MagnusThome/RejsaCAN-ESP32/Code Examples/RejsaCAN v3.x - ESP32-S3 - read rpm over BLE/Arduino IDE settings for ESP32-S3-WROOM-1-N16R8.png

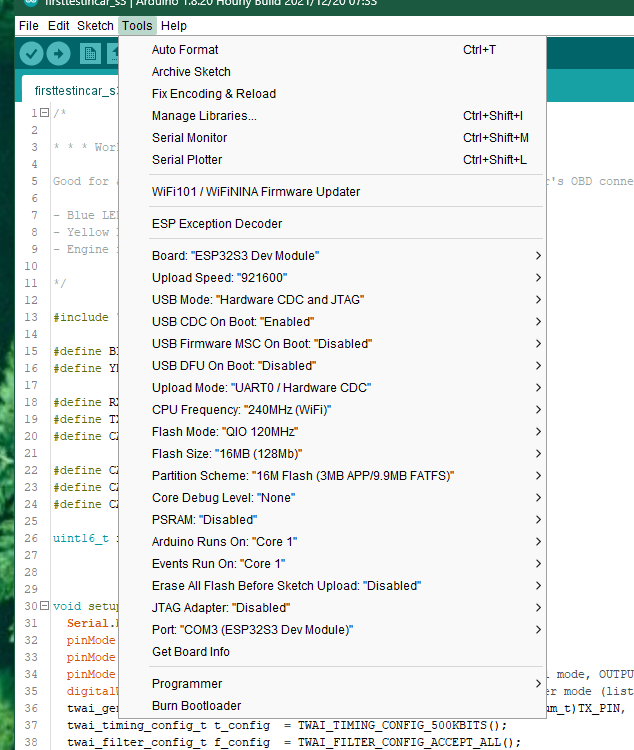
Code Examples/RejsaCAN v3.x - ESP32-S3 - read rpm over BLE/Arduino IDE settings for ESP32-S3-WROOM-1-N16R8.png
