MagnusThome/RejsaCAN-ESP32/Schematics/Schematic_RejsaCAN v2.1.png

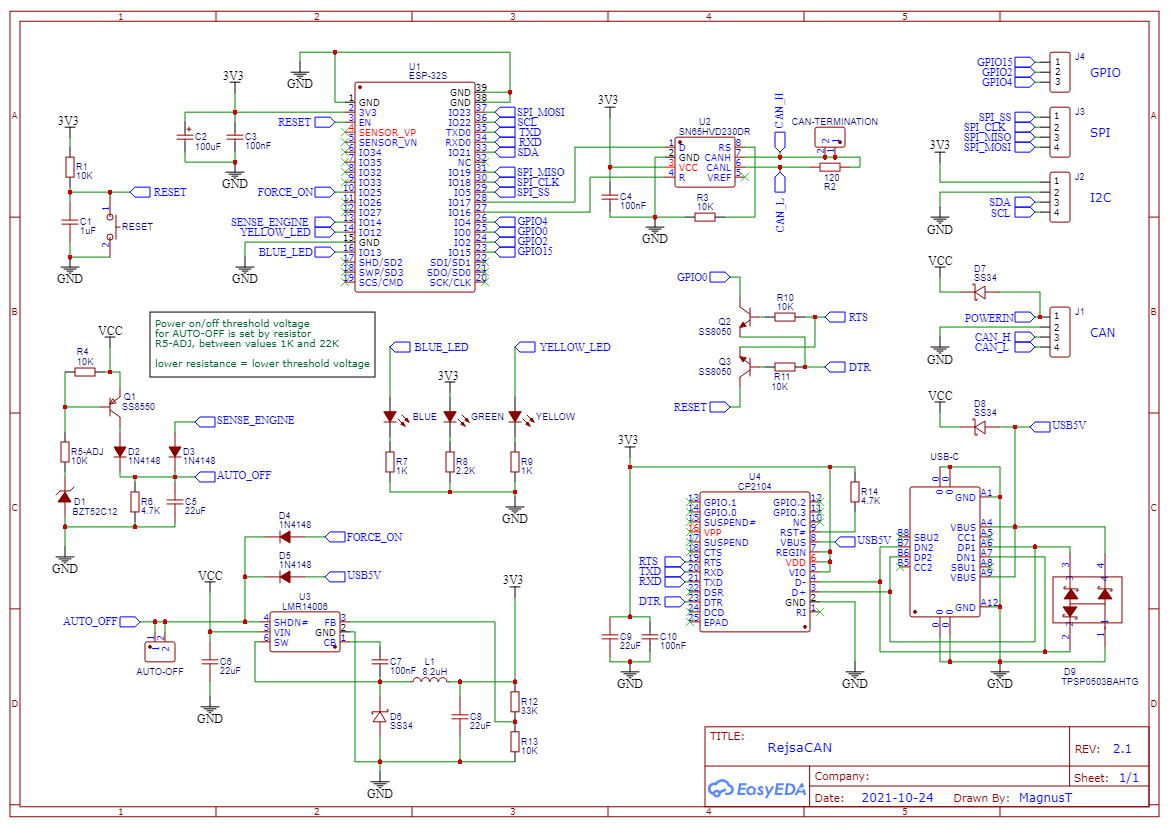
Schematics/Schematic_RejsaCAN v2.1.png
