MagnusThome/RejsaCAN-ESP32/Schematics/Schematic_RejsaCAN v2.2b.png

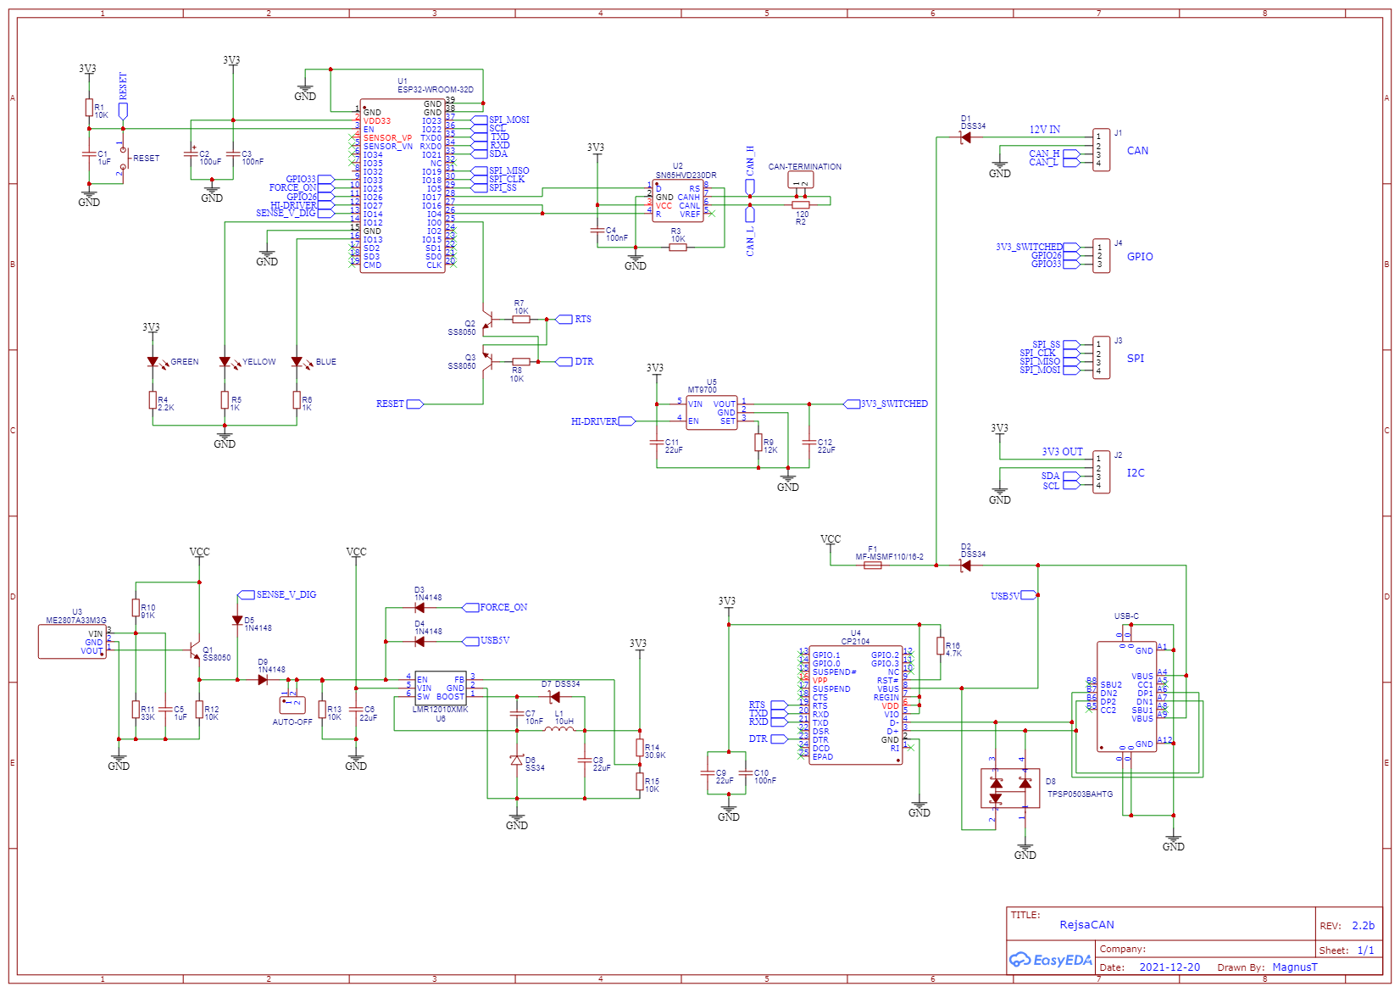
Schematics/Schematic_RejsaCAN v2.2b.png
