MagnusThome/RejsaCAN-ESP32/Schematics/Schematic_RejsaCAN v2.3.png

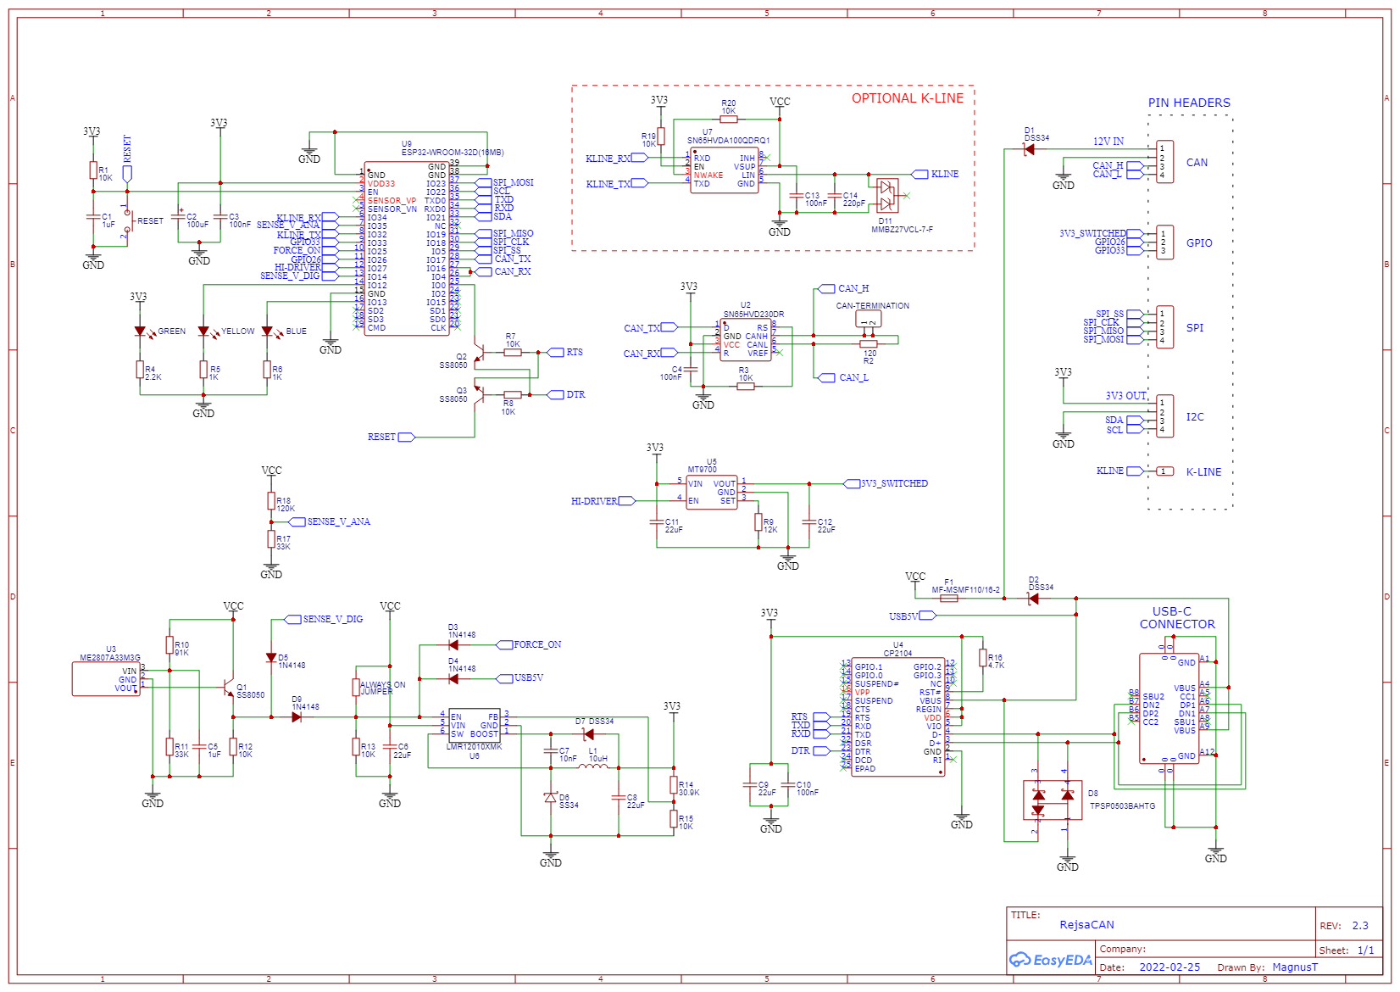
Schematics/Schematic_RejsaCAN v2.3.png
