MagnusThome/RejsaCAN-ESP32/Schematics/Schematic_RejsaCAN v3.0.png

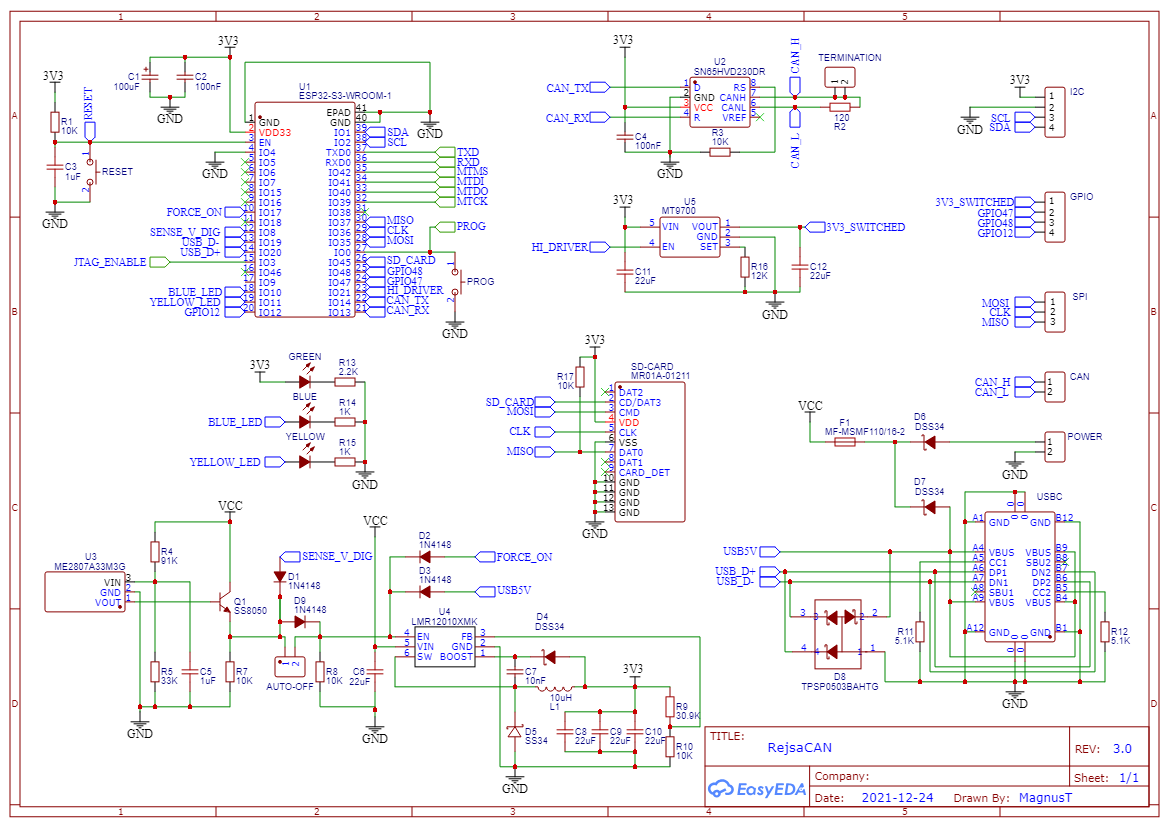
Schematics/Schematic_RejsaCAN v3.0.png
