MagnusThome/RejsaCAN-ESP32/3dprint/Small-flat-housing-LID.stl

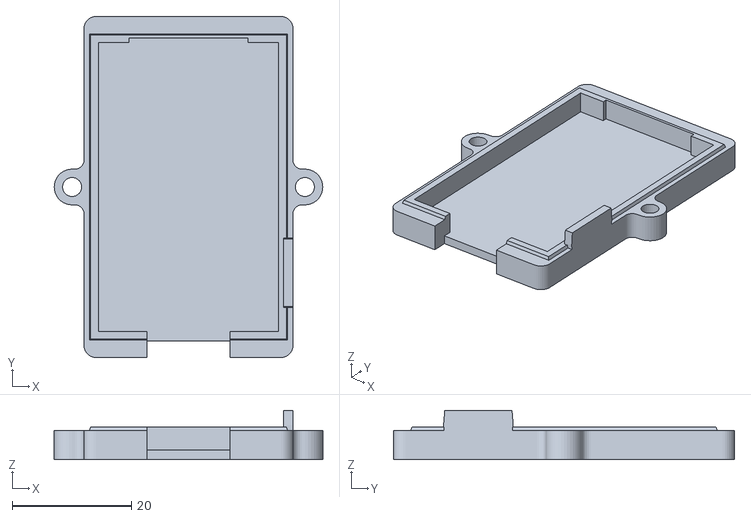
[picture p26: CAD file, 2021-10-26, last stored version]
3dprint/Small-flat-housing-LID.stl
45.1 x 57.2 x 8.30
