MagnusThome/RejsaCAN-ESP32/Code Examples/RejsaCAN v3.x - ESP32-S3 - read rpm over BLE/ble_uart.h

#include <BLEDevice.h>
#include <BLEServer.h>
#include <BLEUtils.h>
#include <BLE2902.h>




#define SERVICE_UUID           "6E400001-B5A3-F393-E0A9-E50E24DCCA9E" // UART service UUID
#define CHARACTERISTIC_UUID_RX "6E400002-B5A3-F393-E0A9-E50E24DCCA9E"
#define CHARACTERISTIC_UUID_TX "6E400003-B5A3-F393-E0A9-E50E24DCCA9E"


BLEServer *pServer = NULL;
BLECharacteristic * pTxCharacteristic;
bool deviceConnected = false;
bool oldDeviceConnected = false;


#define BUFFSIZE 16
char prntbuff[BUFFSIZE];



// --------------------------------------------------

class MyServerCallbacks: public BLEServerCallbacks {
    void onConnect(BLEServer* pServer) {
      deviceConnected = true;
    };
    void onDisconnect(BLEServer* pServer) {
      deviceConnected = false;
    }
};

class MyCallbacks: public BLECharacteristicCallbacks {
    void onWrite(BLECharacteristic *pCharacteristic) {
      std::string rxValue = pCharacteristic->getValue();
      if (rxValue.length() > 0) {
        Serial.print("Received Value: ");
        for (int i = 0; i < rxValue.length(); i++)
          Serial.print(rxValue[i]);
        Serial.println();
      }
    }
};


// --------------------------------------------------

void ble_setup() {
  BLEDevice::init("RejsaCAN UART Service");
  pServer = BLEDevice::createServer();
  pServer->setCallbacks(new MyServerCallbacks());
  BLEService *pService = pServer->createService(SERVICE_UUID);
  pTxCharacteristic = pService->createCharacteristic(CHARACTERISTIC_UUID_TX, BLECharacteristic::PROPERTY_NOTIFY);
  pTxCharacteristic->addDescriptor(new BLE2902());
  BLECharacteristic * pRxCharacteristic = pService->createCharacteristic(CHARACTERISTIC_UUID_RX, BLECharacteristic::PROPERTY_WRITE);
  pRxCharacteristic->setCallbacks(new MyCallbacks());
  pService->start();
  pServer->getAdvertising()->start();
  Serial.println("Started advertising...");
}


// --------------------------------------------------

void ble_loop() {
  unsigned long loopnow = millis();

  // disconnecting, restart advertising
  if (!deviceConnected && oldDeviceConnected) {
    delay(500); // give the bluetooth stack the chance to get things ready
    pServer->startAdvertising();
    oldDeviceConnected = deviceConnected;
    Serial.println("Disconnected. Restarted advertising...");
  }

  // connecting
  if (deviceConnected && !oldDeviceConnected) {
    // do stuff here on connecting
    oldDeviceConnected = deviceConnected;
    Serial.println("Connected");
  }
}


// --------------------------------------------------

void ble_send (uint16_t sendvalue) {
  if (deviceConnected) {
    snprintf(prntbuff, BUFFSIZE, "%d\n", sendvalue);
    pTxCharacteristic->setValue(prntbuff);
    pTxCharacteristic->notify();
    Serial.print("BLE sent: ");
    Serial.println(sendvalue);
  }
}


// --------------------------------------------------
